nuclearcat/ESPFLASHER/docs/usb-routing/after-3d.png

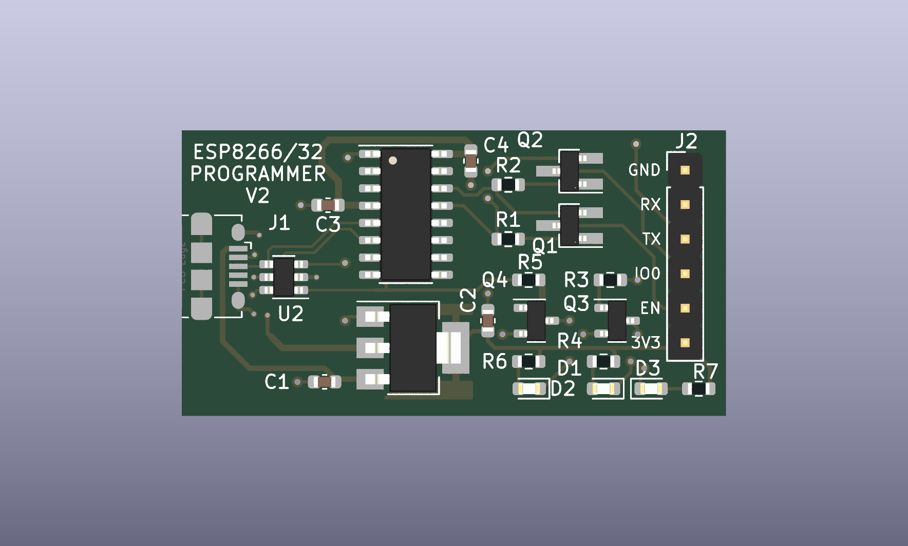
docs/usb-routing/after-3d.png
